alota227/NoiseMonitor/Database and User Display/noisedb.JPG

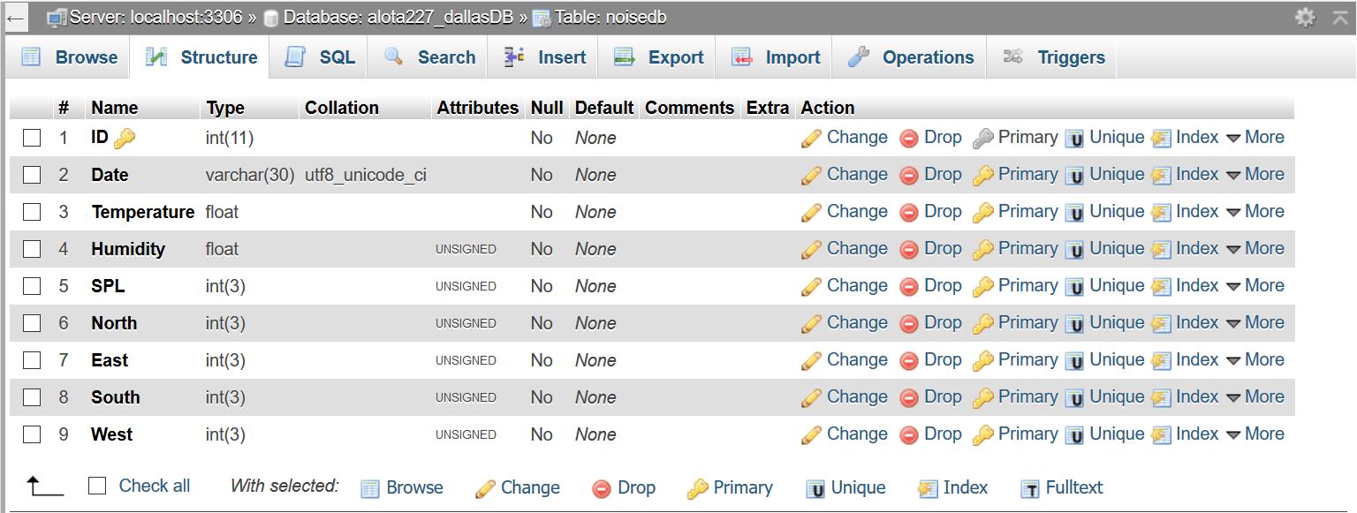
Database and User Display/noisedb.JPG
