alota227/NoiseMonitor/PCB_Design_Eagle/IMG_4662.JPG

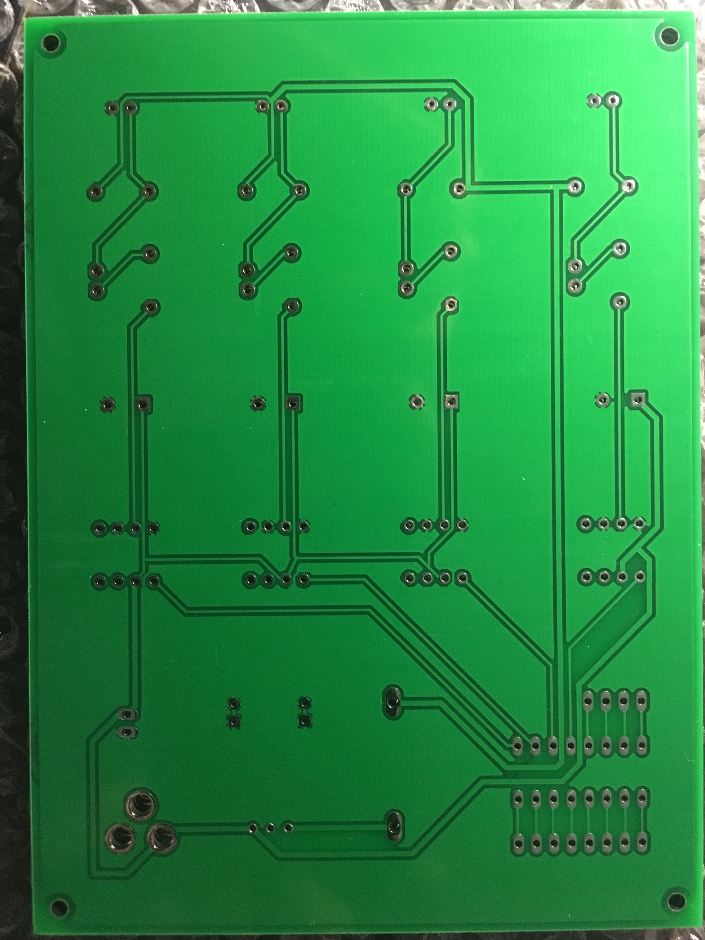
PCB_Design_Eagle/IMG_4662.JPG
