alota227/NoiseMonitor/PCB_Design_Eagle/MicSchema.JPG

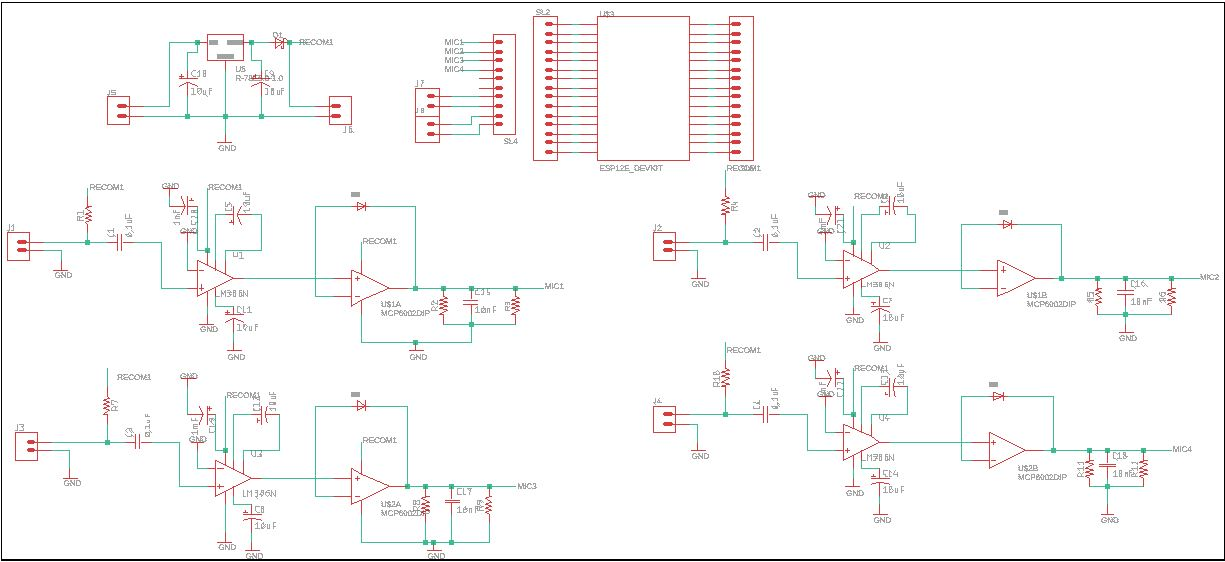
PCB_Design_Eagle/MicSchema.JPG
