alota227/NoiseMonitor/Webserver_Testing/sample_image_website_v2.PNG

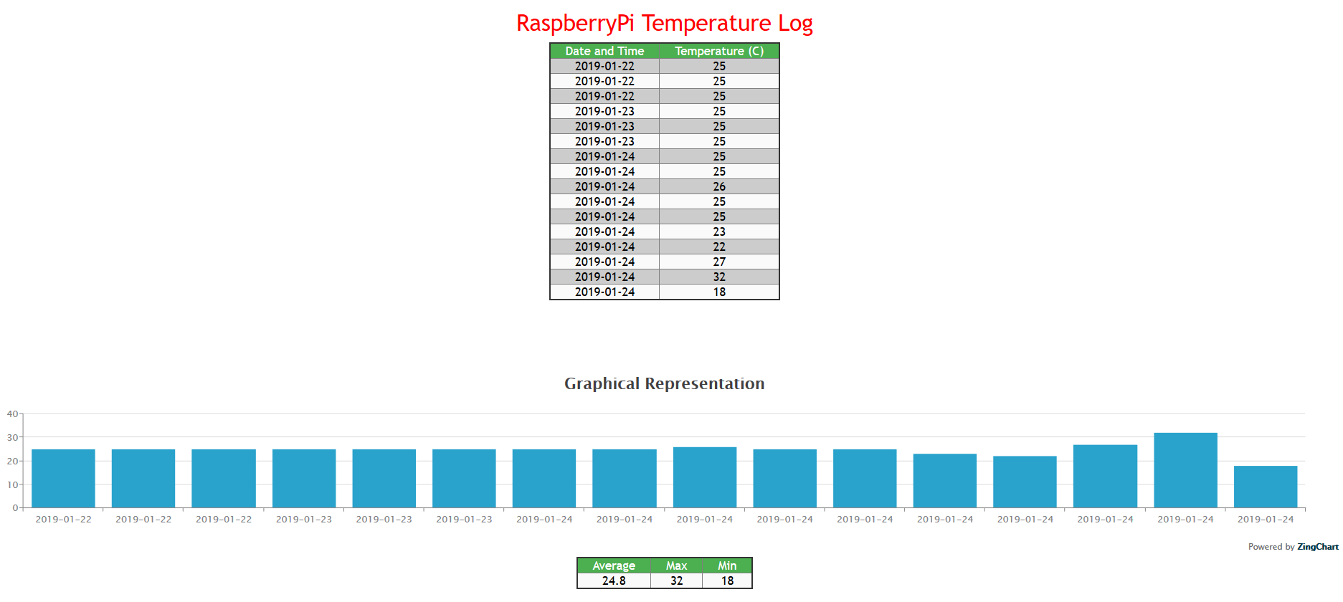
Webserver_Testing/sample_image_website_v2.PNG
